khinds10/SunRiseCatcher/display/imageData.h

const uint8_t imageData[]= {0x00,0x00,0x00,0x34,0x3d,0x38,0x32,0x3a,0x35,0x21,0x28,0x24,0x26,0x2c,0x28,0x36,0x3b,0x38,0x35,0x39,0x36,0x35,0x38,0x35,0x3b,0x3d,0x3b,0x3b,0x3c,0x3b,0x3c,0x3c,0x3b,0x3c,0x3c,0x3b,0x3c,0x3c,0x3b,0x3b,0x3c,0x3b,0x3b,0x3c,0x3b,0x3b,0x3c,0x3b,0x3b,0x3c,0x3b,0x3b,0x3c,0x3b,0x3c,0x3d,0x3c,0x3b,0x3c,0x3b,0x3b,0x3c,0x3b,0x3d,0x3e,0x3d,0x3b,0x3c,0x3b,0x2f,0x30,0x2f,0x21,0x22,0x21,0x18,0x1a,0x19,0x13,0x14,0x13,0x10,0x11,0x10,0x13,0x14,0x13,0x0f,0x10,0x0f,0x0c,0x0d,0x0c,0x11,0x12,0x11,0x0e,0x0e,0x0d,0x0b,0x0c,0x09,0x0c,0x0c,0x09,0x0c,0x0b,0x08,0x0f,0x0e,0x0b,0x0d,0x0c,0x09,0x0b,0x0a,0x07,0x0c,0x0b,0x08,0x08,0x06,0x03,0x0a,0x08,0x05,0x09,0x07,0x04,0x09,0x06,0x03,0x0a,0x07,0x04,0x0d,0x09,0x05,0x0e,0x0a,0x07,0x0f,0x0b,0x08,0x10,0x0b,0x08,0x11,0x0c,0x07,0x11,0x0c,0x06,0x11,0x0b,0x07,0x10,0x0b,0x06,0x10,0x0b,0x07,0x10,0x0c,0x07,0x10,0x0d,0x08,0x11,0x0d,0x08,0x0f,0x0a,0x05,0x10,0x0b,0x05,0x1a,0x14,0x0e,0x27,0x20,0x19,0x2a,0x23,0x1c,0x26,0x1e,0x16,0x25,0x1d,0x15,0x27,0x21,0x1a,0x1e,0x1c,0x18,0x06,0x06,0x04,0x05,0x05,0x03,0x04,0x04,0x02,0x02,0x02,0x01,0x05,0x05,0x04,0x02,0x02,0x01,0x05,0x05,0x03,0x04,0x03,0x02,0x04,0x03,0x02,0x04,0x03,0x03,0x03,0x03,0x03,0x03,0x03,0x03,0x03,0x03,0x02,0x03,0x03,0x02,0x03,0x03,0x02,0x03,0x03,0x03,0x03,0x03,0x02,0x03,0x03,0x02,0x05,0x05,0x04,0x05,0x05,0x03,0x04,0x04,0x03,0x05,0x05,0x03,0x07,0x06,0x05,0x07,0x06,0x03,0x07,0x06,0x03,0x07,0x06,0x03,0x07,0x06,0x04,0x08,0x07,0x04,0x09,0x08,0x05,0x0a,0x08,0x05,0x0a,0x09,0x05,0x0b,0x0a,0x06,0x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
16,0x19,0x15,0x21,0x24,0x20,0x27,0x2e,0x2a,0x2e,0x34,0x30,0x2e,0x34,0x30,0x35,0x3b,0x37,0x39,0x3d,0x3a,0x37,0x3a,0x38,0x3c,0x3f,0x3d,0x3a,0x3d,0x3b,0x3a,0x3c,0x3a,0x3b,0x3b,0x3a,0x3b,0x3b,0x3b,0x3b,0x3b,0x3b,0x3c,0x3c,0x3b,0x3c,0x3c,0x3b,0x3c,0x3c,0x3b,0x3c,0x3c,0x3b,0x3c,0x3d,0x3c,0x3b,
