khinds10/SunRiseCatcher/documentation/digole-driver/imageData.h

const uint8_t imageData[]= {0x00,0x00,0x00,0x37,0x39,0x33,0x3d,0x3f,0x39,0x3b,0x3d,0x37,0x21,0x23,0x1d,0x15,0x16,0x11,0x14,0x16,0x10,0x17,0x18,0x12,0x15,0x16,0x10,0x15,0x16,0x0f,0x14,0x15,0x0f,0x14,0x15,0x0e,0x14,0x15,0x0e,0x15,0x15,0x0f,0x15,0x16,0x0f,0x16,0x17,0x10,0x17,0x17,0x10,0x18,0x17,0x10,0x16,0x15,0x0e,0x16,0x15,0x0d,0x18,0x16,0x0f,0x19,0x16,0x0f,0x17,0x15,0x0d,0x18,0x15,0x0e,0x1a,0x18,0x10,0x1a,0x17,0x0e,0x1a,0x17,0x0e,0x1c,0x17,0x0f,0x1c,0x18,0x0f,0x1e,0x19,0x0f,0x1f,0x1a,0x11,0x21,0x1b,0x12,0x21,0x1c,0x12,0x25,0x20,0x15,0x26,0x22,0x17,0x29,0x25,0x1b,0x27,0x24,0x1b,0x2c,0x2a,0x22,0x18,0x17,0x10,0x07,0x06,0x01,0x07,0x06,0x02,0x05,0x05,0x02,0x04,0x05,0x03,0x04,0x05,0x03,0x04,0x05,0x03,0x04,0x05,0x03,0x04,0x05,0x03,0x04,0x05,0x04,0x04,0x05,0x04,0x04,0x04,0x02,0x04,0x04,0x02,0x04,0x04,0x02,0x04,0x04,0x02,0x04,0x04,0x02,0x03,0x04,0x02,0x03,0x03,0x02,0x03,0x03,0x02,0x02,0x02,0x01,0x05,0x05,0x03,0x06,0x07,0x05,0x06,0x06,0x05,0x05,0x05,0x04,0x04,0x05,0x03,0x04,0x04,0x02,0x03,0x03,0x01,0x03,0x03,0x00,0x03,0x04,0x00,0x04,0x05,0x02,0x05,0x05,0x02,0x05,0x05,0x02,0x05,0x05,0x02,0x07,0x06,0x03,0x07,0x06,0x02,0x0a,0x08,0x04,0x06,0x05,0x00,0x0d,0x0b,0x03,0x29,0x28,0x1e,0x2a,0x29,0x1c,0x31,0x30,0x22,0x30,0x2f,0x1f,0x2e,0x2d,0x1f,0x2c,0x2a,0x21,0x29,0x28,0x20,0x30,0x30,0x28,0x32,0x33,0x2b,0x29,0x2b,0x24,0x28,0x2b,0x24,0x2b,0x2f,0x27,0x25,0x2a,0x22,0x2a,0x2f,0x27,0x27,0x2d,0x24,0x25,0x2b,0x20,0x25,0x2a,0x1e,0x26,0x2b,0x1e,0x22,0x27,0x18,0x15,0x19,0x0a,0x09,0x0c,0x00,0x03,0x04,0x00,0x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
