khinds10/SunRiseCatcher/documentation/digole-driver/imageData-sample.h

const uint8_t imageData[]=
{
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
};
